Queens-Rocket-Engineering-Team/avionics-propulsion-integration/Schematics/upper_lc_board/models/282834-3.step

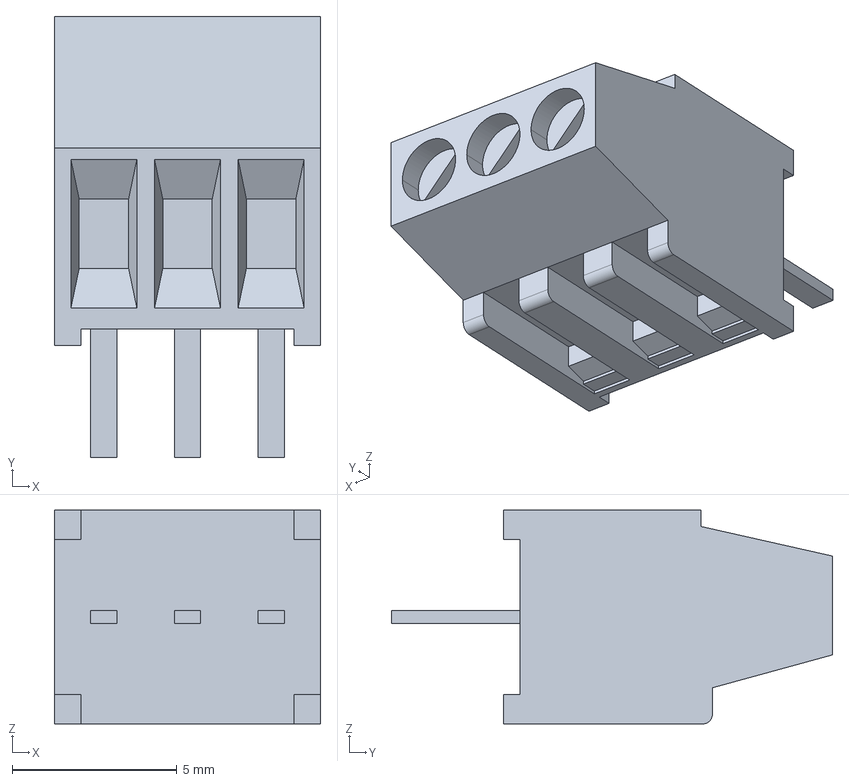
[picture p16: CAD file, 2025-11-26]
Schematics/upper_lc_board/models/282834-3.step
8.08 x 13.4 x 6.50 mm
