Queens-Rocket-Engineering-Team/avionics-propulsion-integration/Schematics/upper_lc_board/models/530480210.step

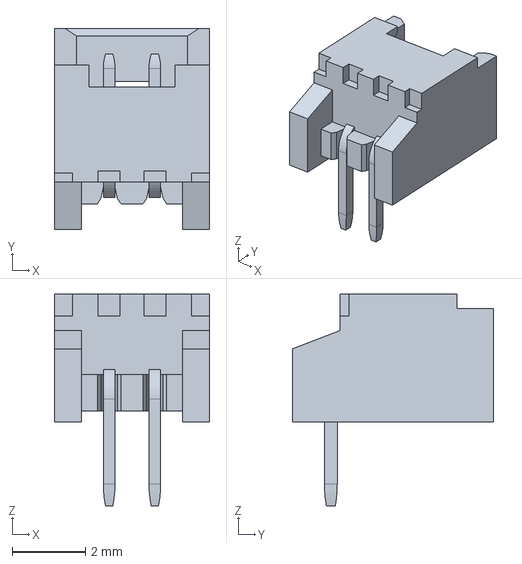
[picture p17: CAD file, 2025-11-26]
Schematics/upper_lc_board/models/530480210.step
4.25 x 5.50 x 5.80 mm
