Queens-Rocket-Engineering-Team/avionics-propulsion-integration/Schematics/upper_lc_board/models/53048-0310.step

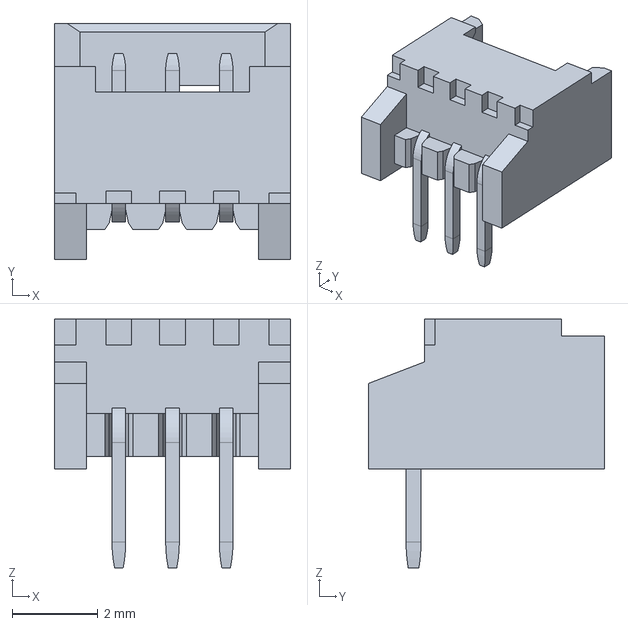
[picture p18: CAD file, 2025-11-26]
Schematics/upper_lc_board/models/53048-0310.step
5.50 x 5.50 x 5.80 mm
